gavinlyonsrepo/Arduino_FM_radio/doc/eagle/fm_radio.sch

## EAGLE design doc/eagle/fm_radio.sch (2019-03-01)

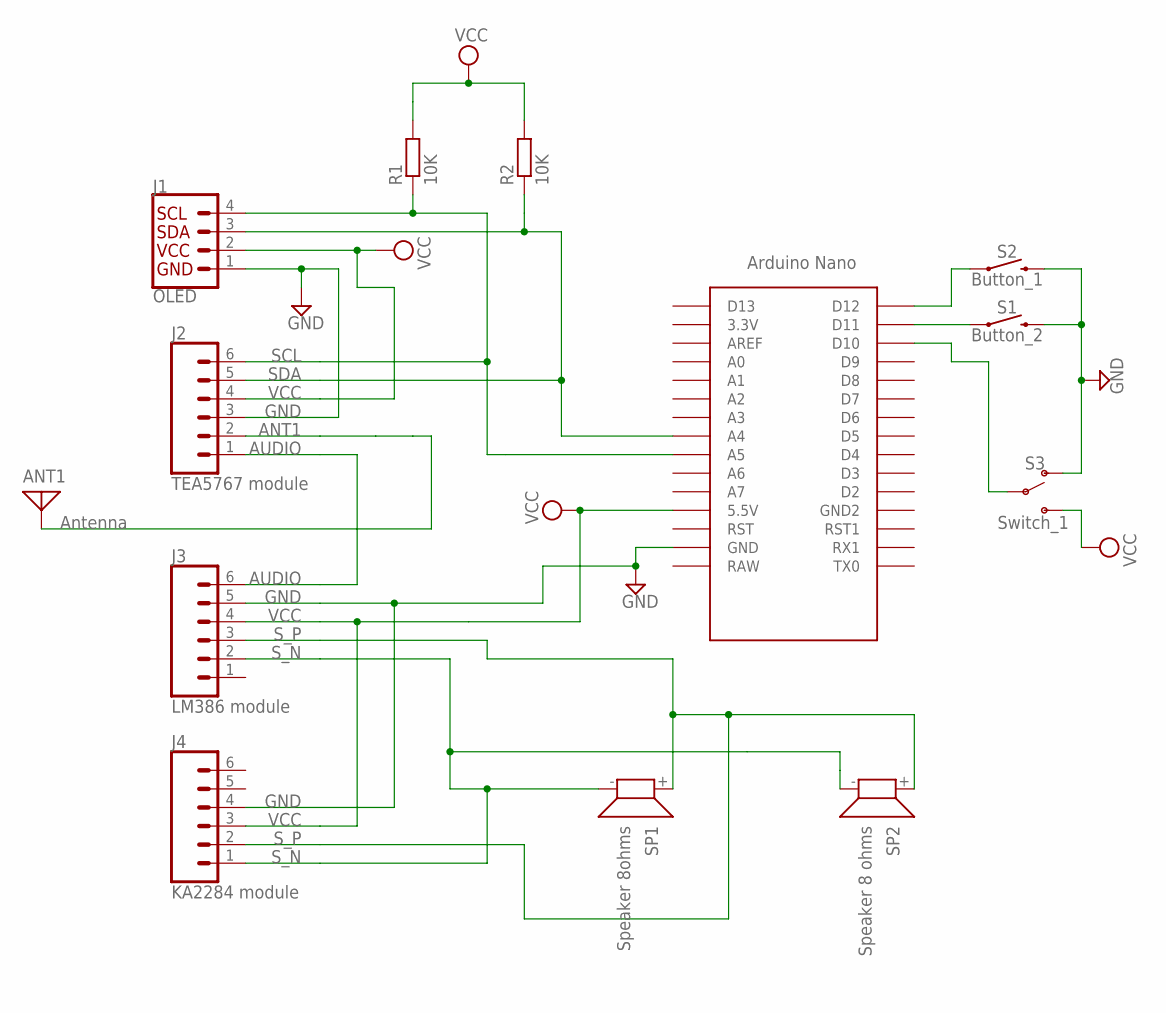
[picture p7: schematic fm_radio.sch]

Parts:
ANT1: Antenna; PAD-01
J1: OLED; 1X04_NO_SILK
J2: TEA5767 module; 1X06_1.27MM
J3: LM386 module; 1X06_1.27MM
J4: KA2284 module; 1X06_1.27MM
R1, R2: 10K; R0603
S1: Button_2; TACTILE_SWITCH_PTH_6.0MM
S2: Button_1; TACTILE_SWITCH_PTH_6.0MM
S3: Switch_1; SWITCH_DPDT_SMD_AYZ0202
SP1: Speaker 8ohms; SMS-1308MS-2-R
SP2: Speaker 8 ohms; SMS-1308MS-2-R
U$1: NANO

Connections:
ANT1: ANT1.1, J2.2
AUDIO: J2.1, J3.6
GND: J1.1, J2.3, J3.5, J4.4, S1.3 (2), S2.3 (2), S3.1 (O), U$1.GND
unnamed: S3.2, U$1.D10
unnamed: S1.1, U$1.D11
unnamed: S2.1, U$1.D12
SCL: J1.4, J2.6, R1.1, U$1.A5
SDA: J1.3, J2.5, R2.1, U$1.A4
S_N: J3.2, J4.1, SP1.- (2), SP2.- (2)
S_P: J3.3, J4.2, SP1.+ (1), SP2.+ (1)
VCC: J1.2, J2.4, J3.4, J4.3, R1.2, R2.2, S3.3 (S), U$1.5V (5.5V)
